romildodcm/plataforma-de-dados-meteorologicos/databases_export_sample/ws02-via-sd/readme.png

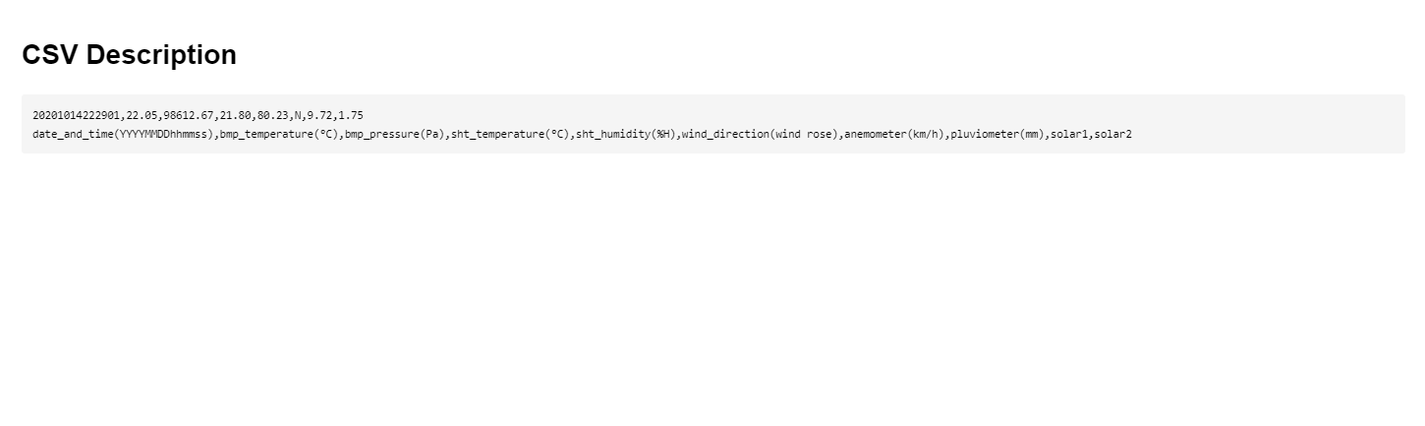
databases_export_sample/ws02-via-sd/readme.png
