romildodcm/plataforma-de-dados-meteorologicos/img/baia-de-instrumentos.jpg

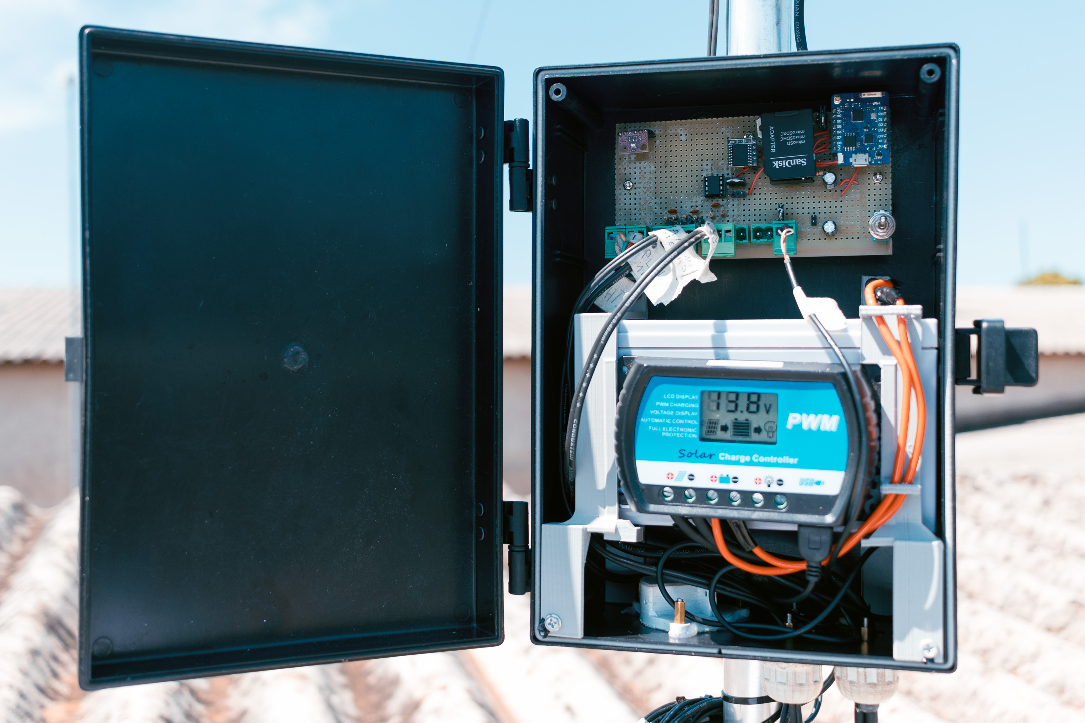
img/baia-de-instrumentos.jpg
