romildodcm/plataforma-de-dados-meteorologicos/img/circuito.jpg

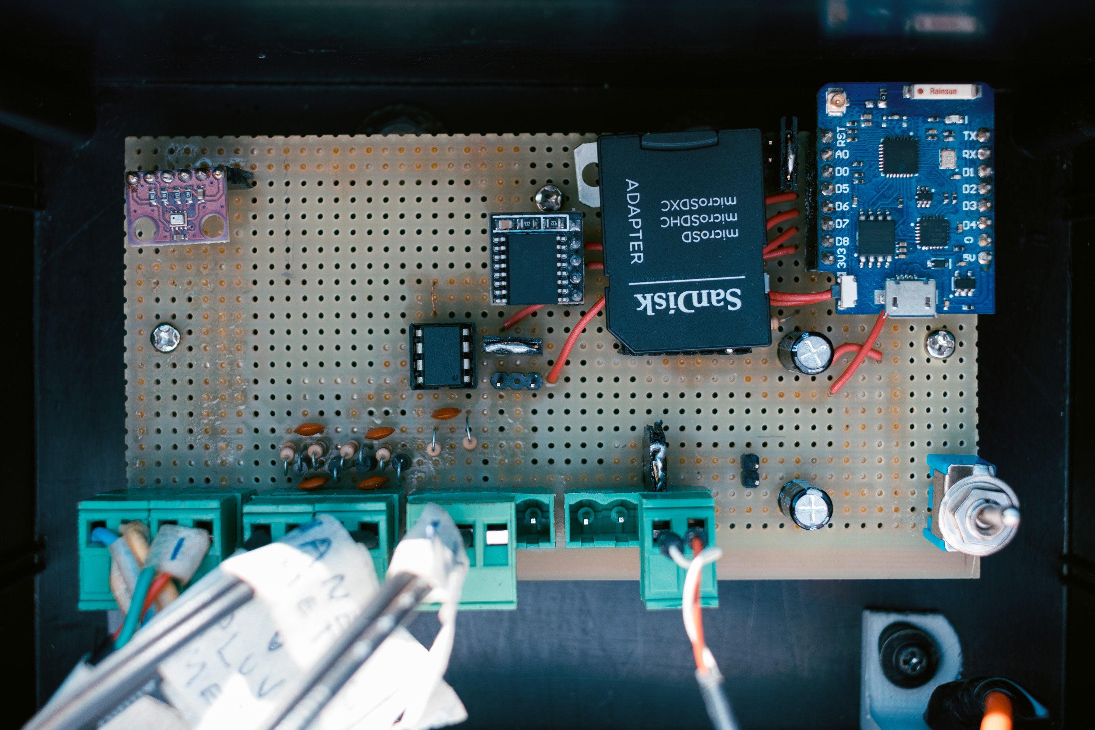
img/circuito.jpg
