romildodcm/plataforma-de-dados-meteorologicos/img/grupo.png

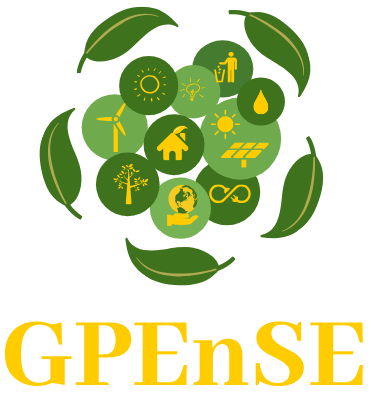
img/grupo.png
