romildodcm/plataforma-de-dados-meteorologicos/weather-station/hardware/esquema-eletrico/rev3 - placa estação 2/IMG_20210731_115449.jpg

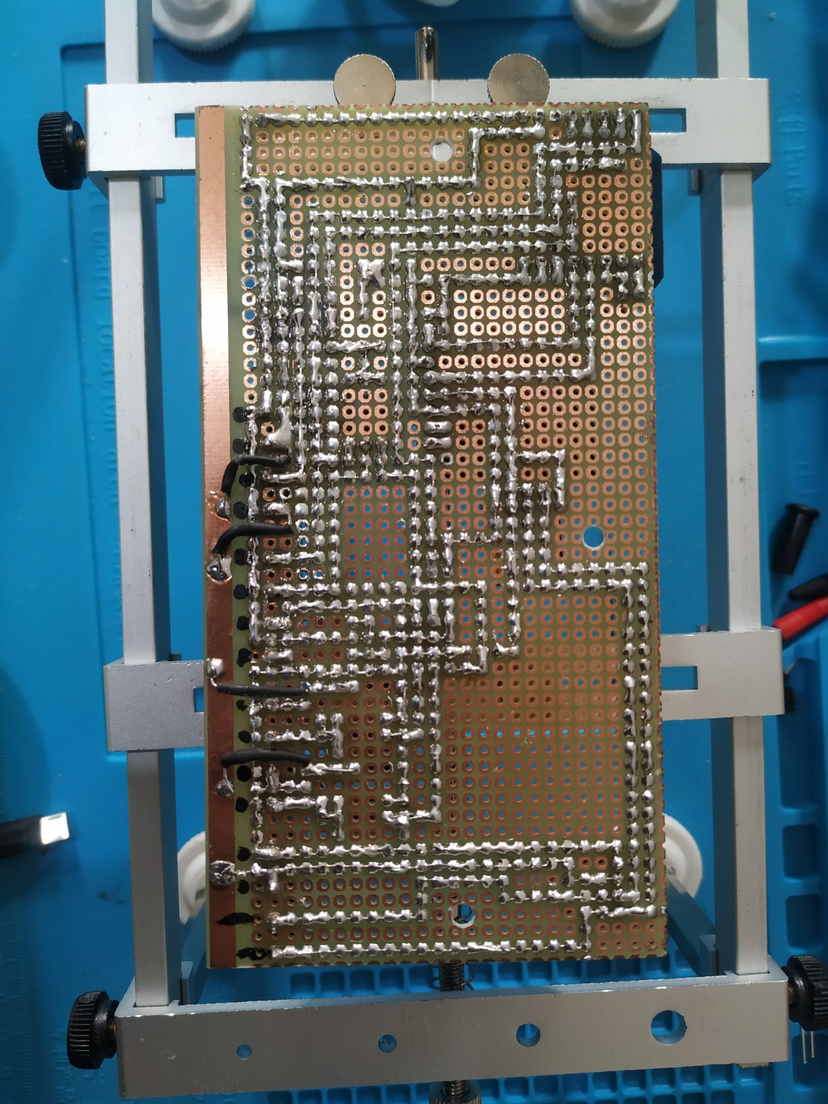
weather-station/hardware/esquema-eletrico/rev3 - placa estação 2/IMG_20210731_115449.jpg
