romildodcm/plataforma-de-dados-meteorologicos/weather-station/hardware/esquema-eletrico/rev 1  - Placa estação 1/IMG_20210803_170211.jpg

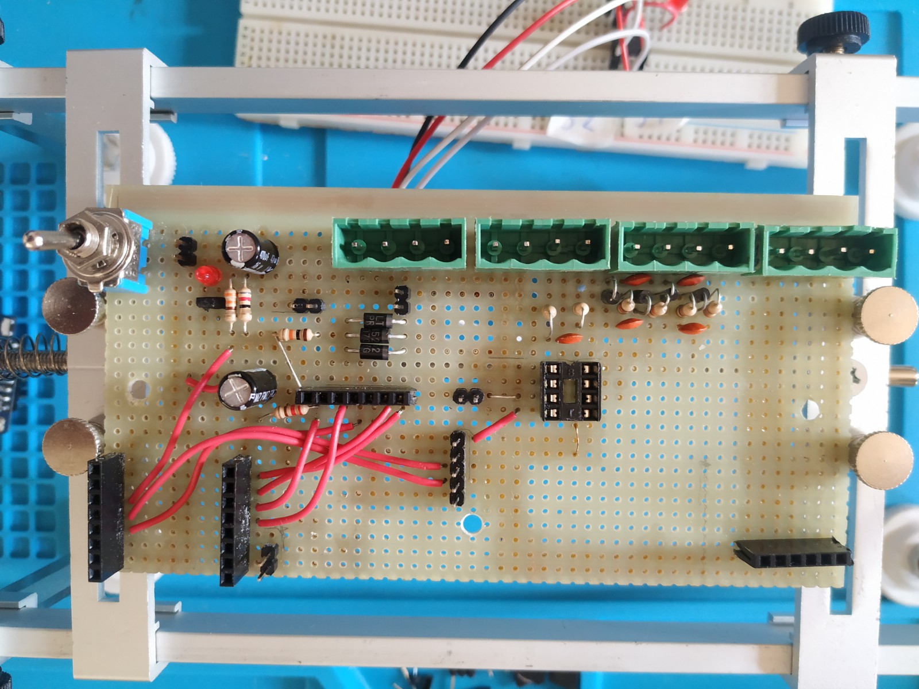
weather-station/hardware/esquema-eletrico/rev 1 - Placa estação 1/IMG_20210803_170211.jpg
