romildodcm/plataforma-de-dados-meteorologicos/weather-station/hardware/esquema-eletrico/rev 1  - Placa estação 1/IMG_20210803_170634.jpg

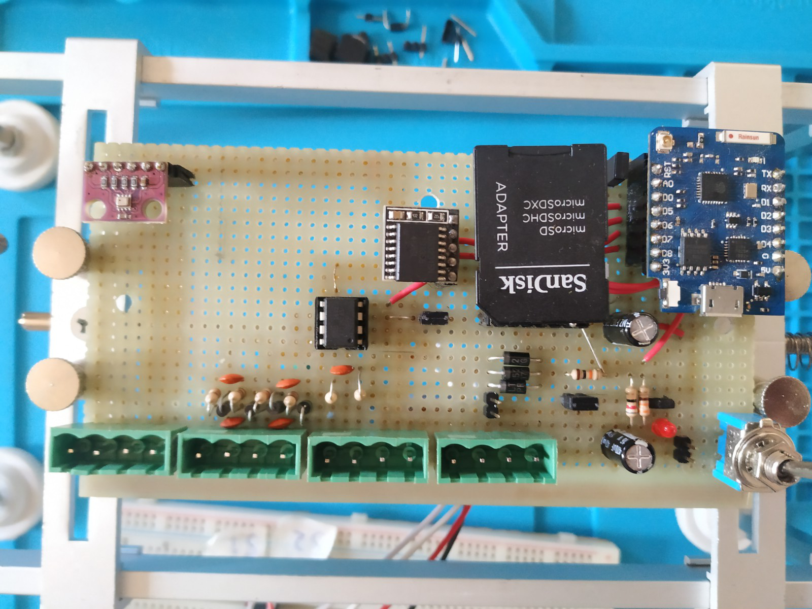
weather-station/hardware/esquema-eletrico/rev 1 - Placa estação 1/IMG_20210803_170634.jpg
